MOSH-Insa-Toulouse/2024-2025-4GP-adele080402-usernameB/Images Projet/application/Écran_app_graphe.png

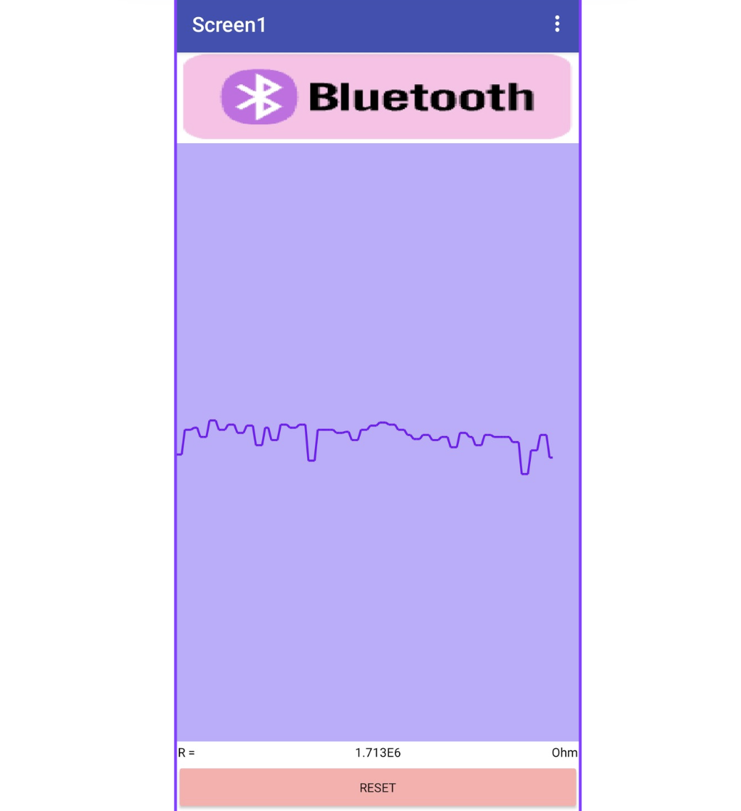
Images Projet/application/Écran_app_graphe.png
