MOSH-Insa-Toulouse/2024-2025-4GP-adele080402-usernameB/Images Projet/Écran_accueil_OLED.png

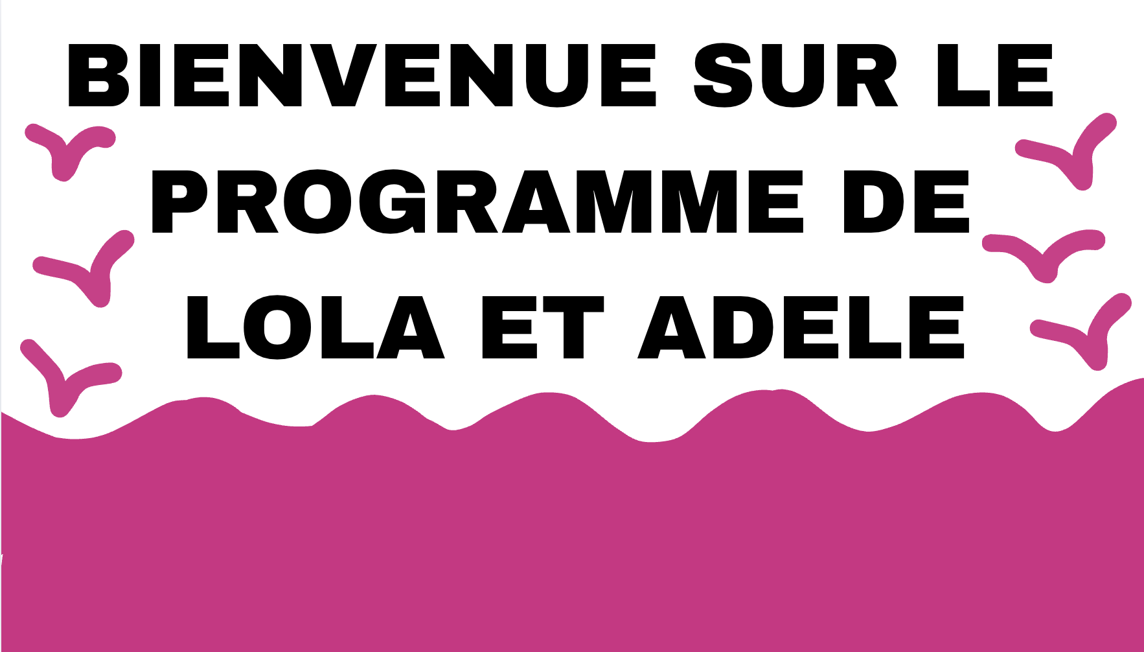
Images Projet/Écran_accueil_OLED.png
