MOSH-Insa-Toulouse/2024-2025-4GP-adele080402-usernameB/Images Projet/Photos_kicad/Schematique_kicad.png

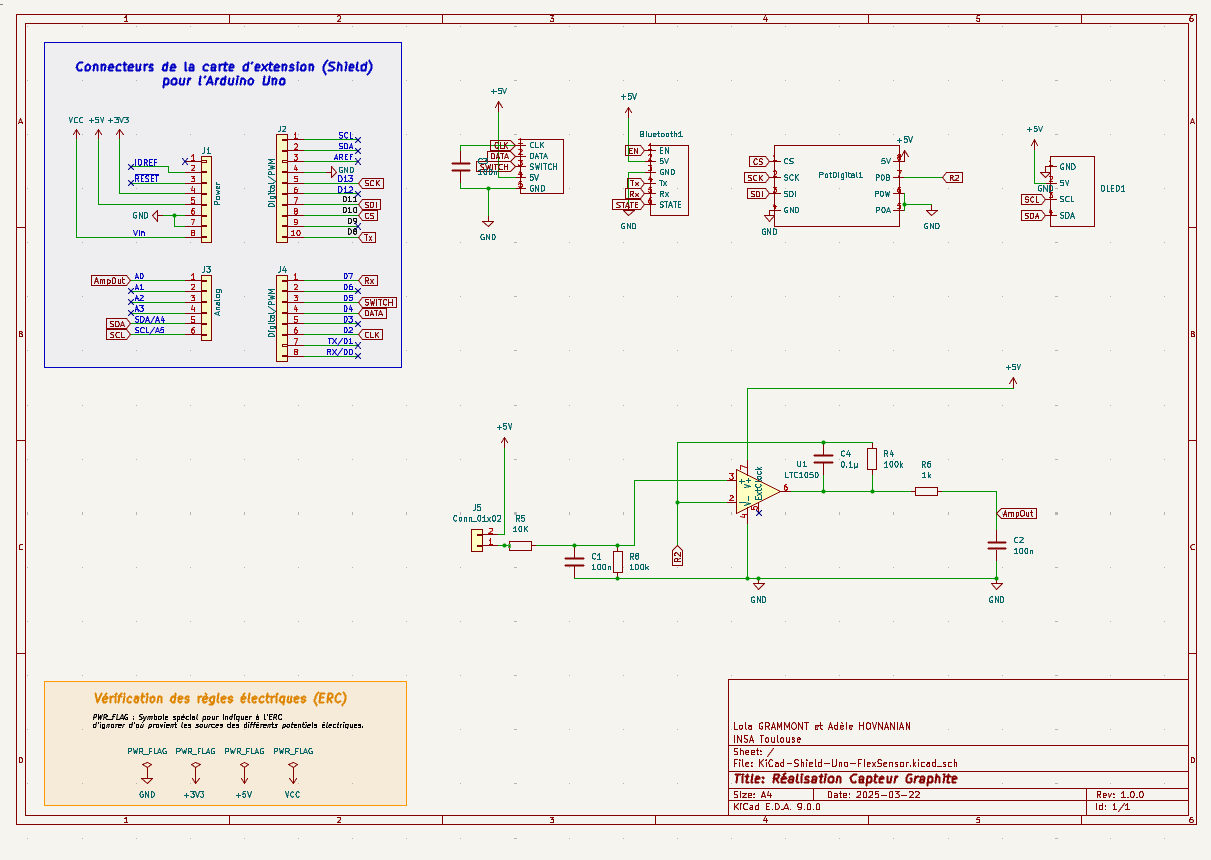
Images Projet/Photos_kicad/Schematique_kicad.png
