MOSH-Insa-Toulouse/2024-2025-4GP-adele080402-usernameB/Images Projet/montage avec capteur image.PNG

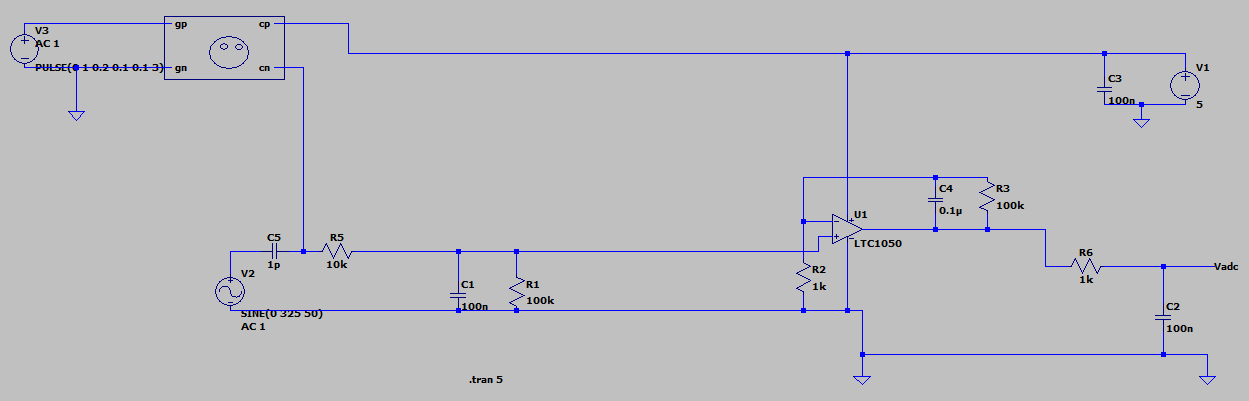
Images Projet/montage avec capteur image.PNG
