MOSH-Insa-Toulouse/2024-2025-4GP-adele080402-usernameB/Images Projet/Photos_kicad/Montage_3D.png

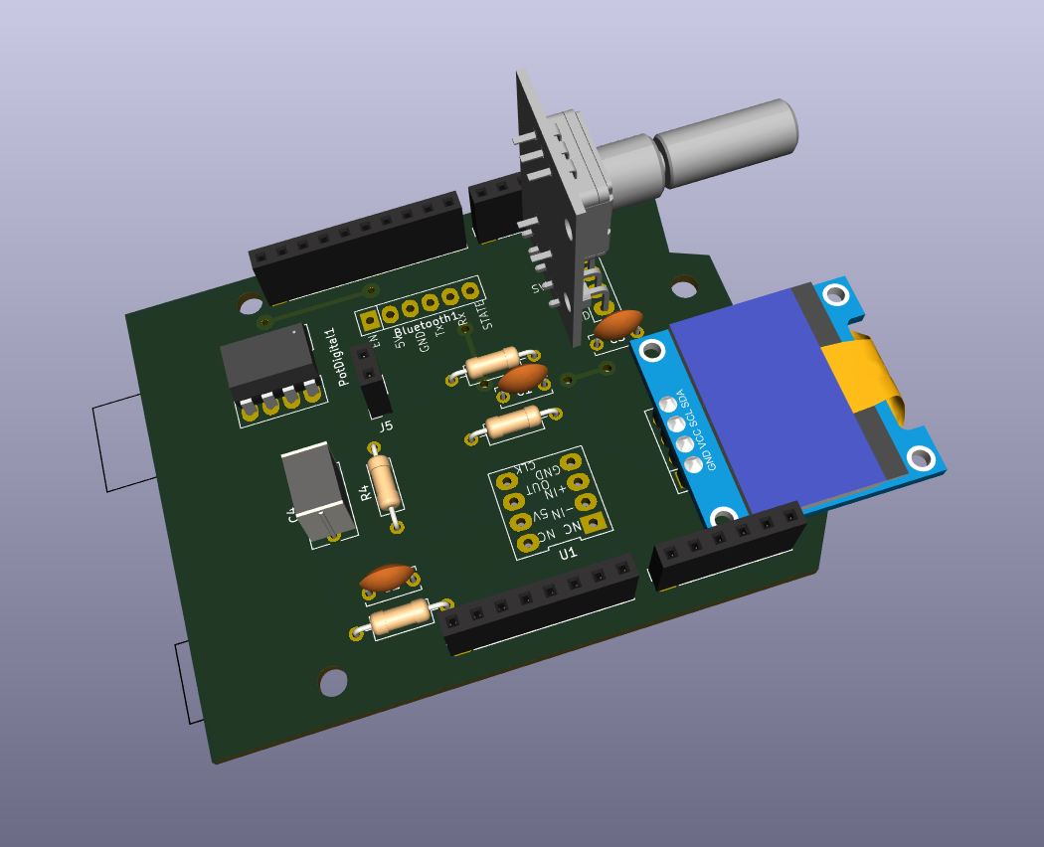
Images Projet/Photos_kicad/Montage_3D.png
